edwardfoofoo14/ALICE-keyboard-/PCB/3d/keycap/DSA_2u.step

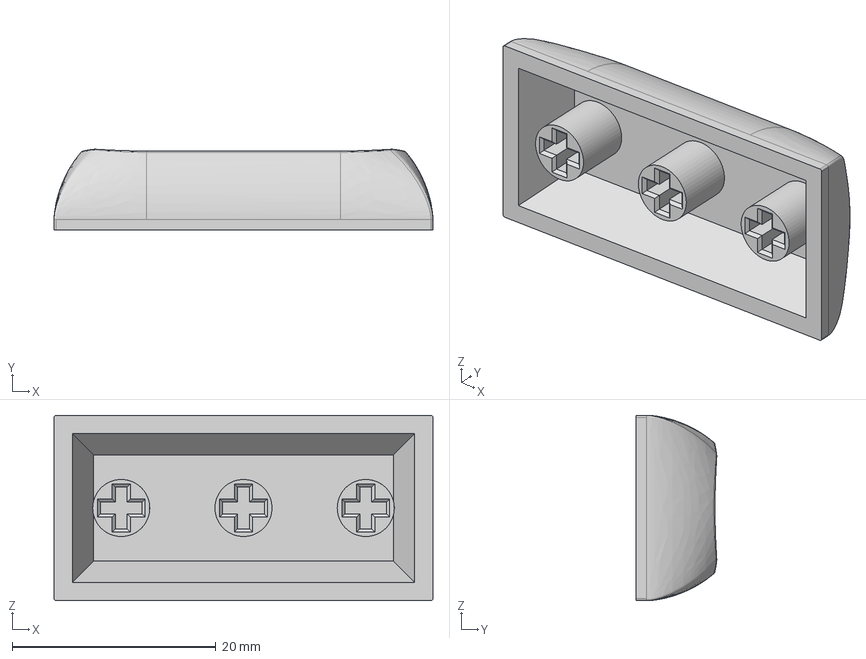
[picture p20: CAD file, 2026-01-05]
PCB/3d/keycap/DSA_2u.step
37.2 x 7.91 x 18.2 mm
