edwardfoofoo14/ALICE-keyboard-/PCB/3d/switch.step

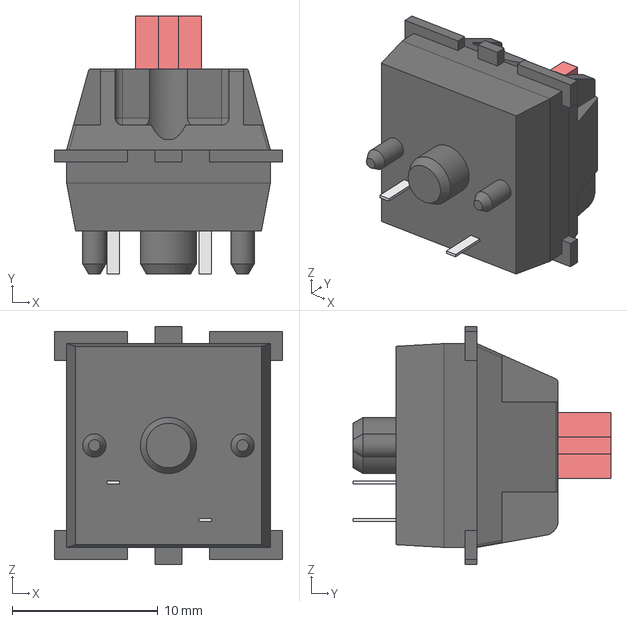
[picture p21: CAD file, 2026-01-05]
PCB/3d/switch.step
15.6 x 17.7 x 16.3 mm
