edwardfoofoo14/ALICE-keyboard-/production/LaserCut/plate 8.dxf

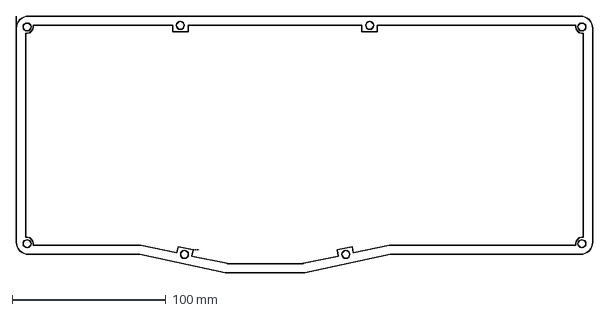
[picture p22: CAD file, 2025-12-23]
production/LaserCut/plate 8.dxf
375.0 x 167.0 mm
