edwardfoofoo14/ALICE-keyboard-/PCB/3d/keycap/DSA_2.75u.step

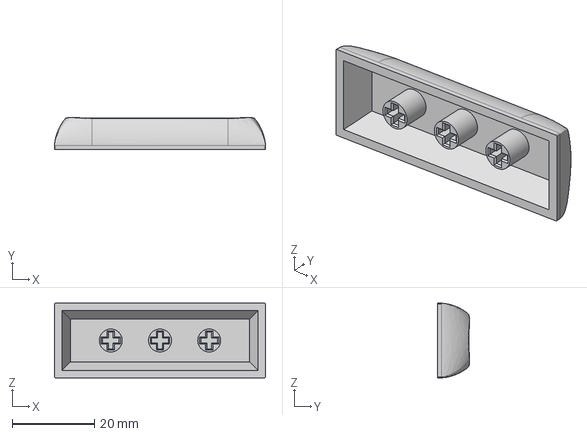
[picture p23: CAD file, 2026-01-05]
PCB/3d/keycap/DSA_2.75u.step
51.5 x 7.91 x 18.2 mm
