edwardfoofoo14/ALICE-keyboard-/PCB/3d/TS-1187A-B-A-B.step

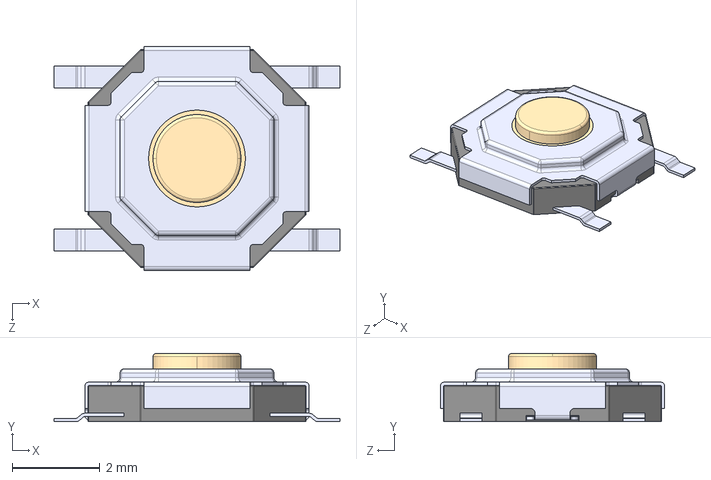
[picture p24: CAD file, 2026-01-05]
PCB/3d/TS-1187A-B-A-B.step
6.50 x 1.55 x 5.10 mm
