edwardfoofoo14/ALICE-keyboard-/PCB/3d/keycap/DSA_1.25u.step

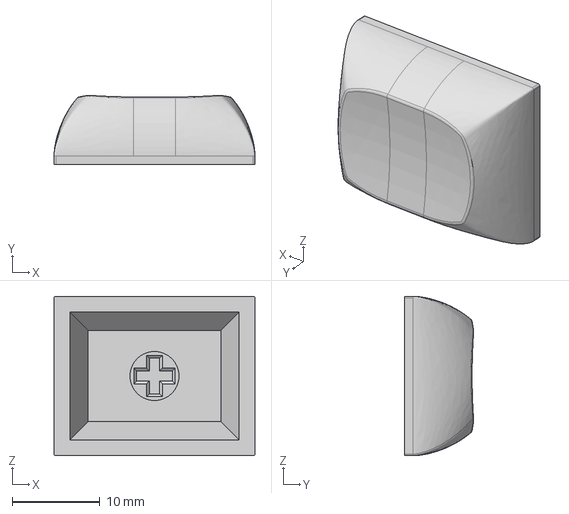
[picture p25: CAD file, 2026-01-05]
PCB/3d/keycap/DSA_1.25u.step
22.9 x 7.91 x 18.2 mm
