edwardfoofoo14/ALICE-keyboard-/PCB/3d/stabilizer.STEP

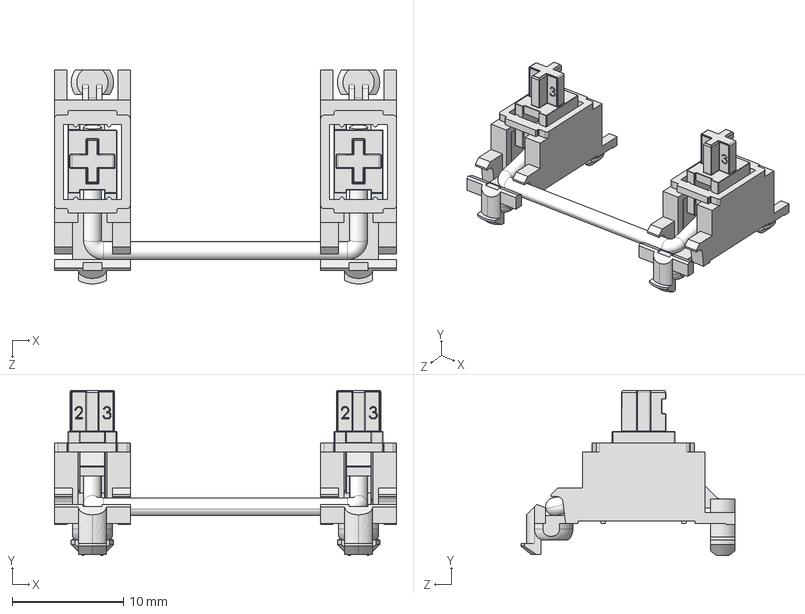
[picture p26: CAD file, 2026-01-05]
PCB/3d/stabilizer.STEP
30.7 x 14.9 x 19.2 mm
mx Stabilizer base 16828 x 2
mx Stabilizer key 16828 x 2
metal stick 16828
