edwardfoofoo14/ALICE-keyboard-/production/LaserCut/plate 10.dxf

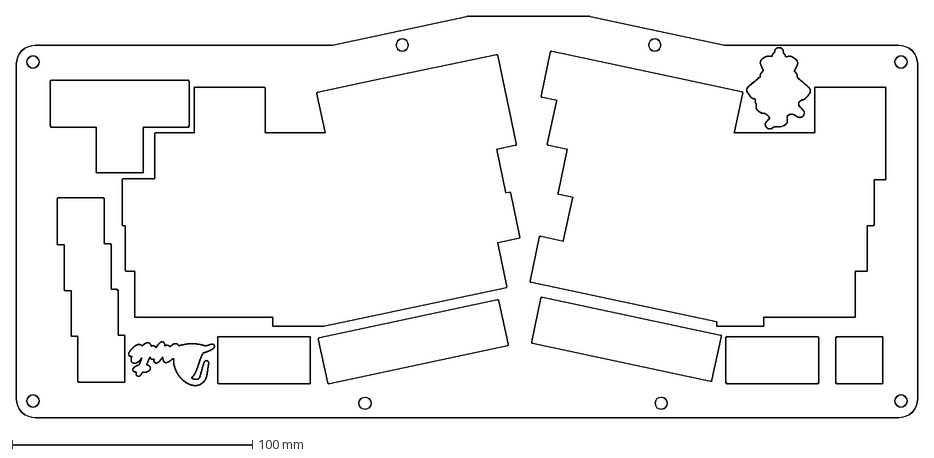
[picture p28: CAD file, 2025-12-23]
production/LaserCut/plate 10.dxf
375.0 x 167.0 mm
