edwardfoofoo14/ALICE-keyboard-/PCB/thisoneinitiald.kicad_sch

## KiCad design PCB/thisoneinitiald.kicad_sch (2026-01-20)

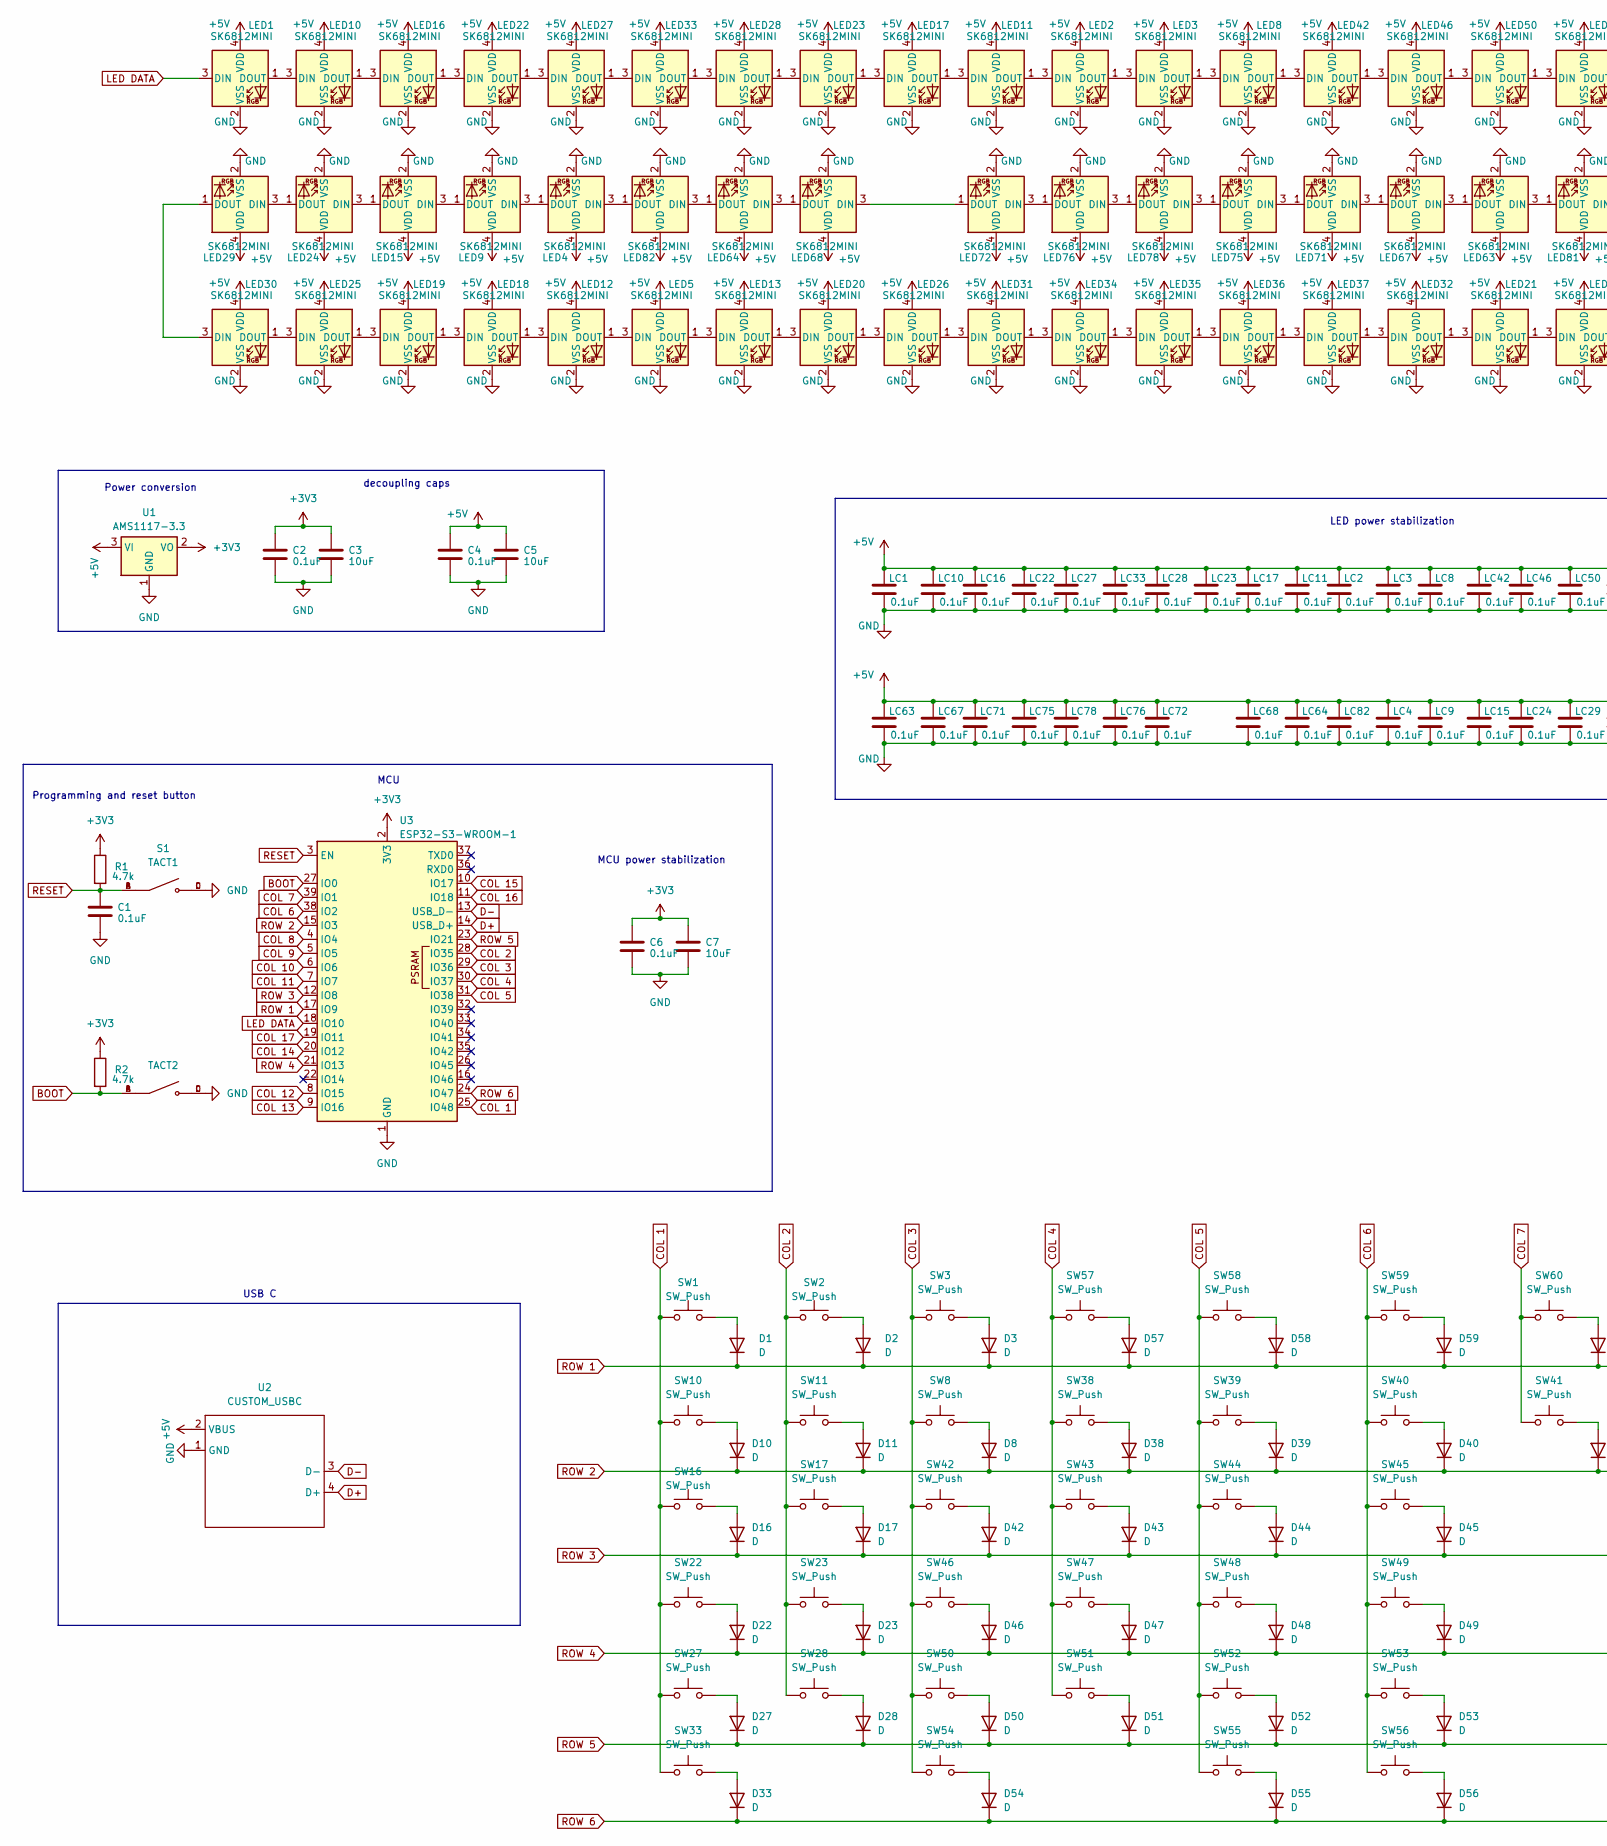
[picture p30: schematic thisoneinitiald.kicad_sch, part in row 1, column 1]

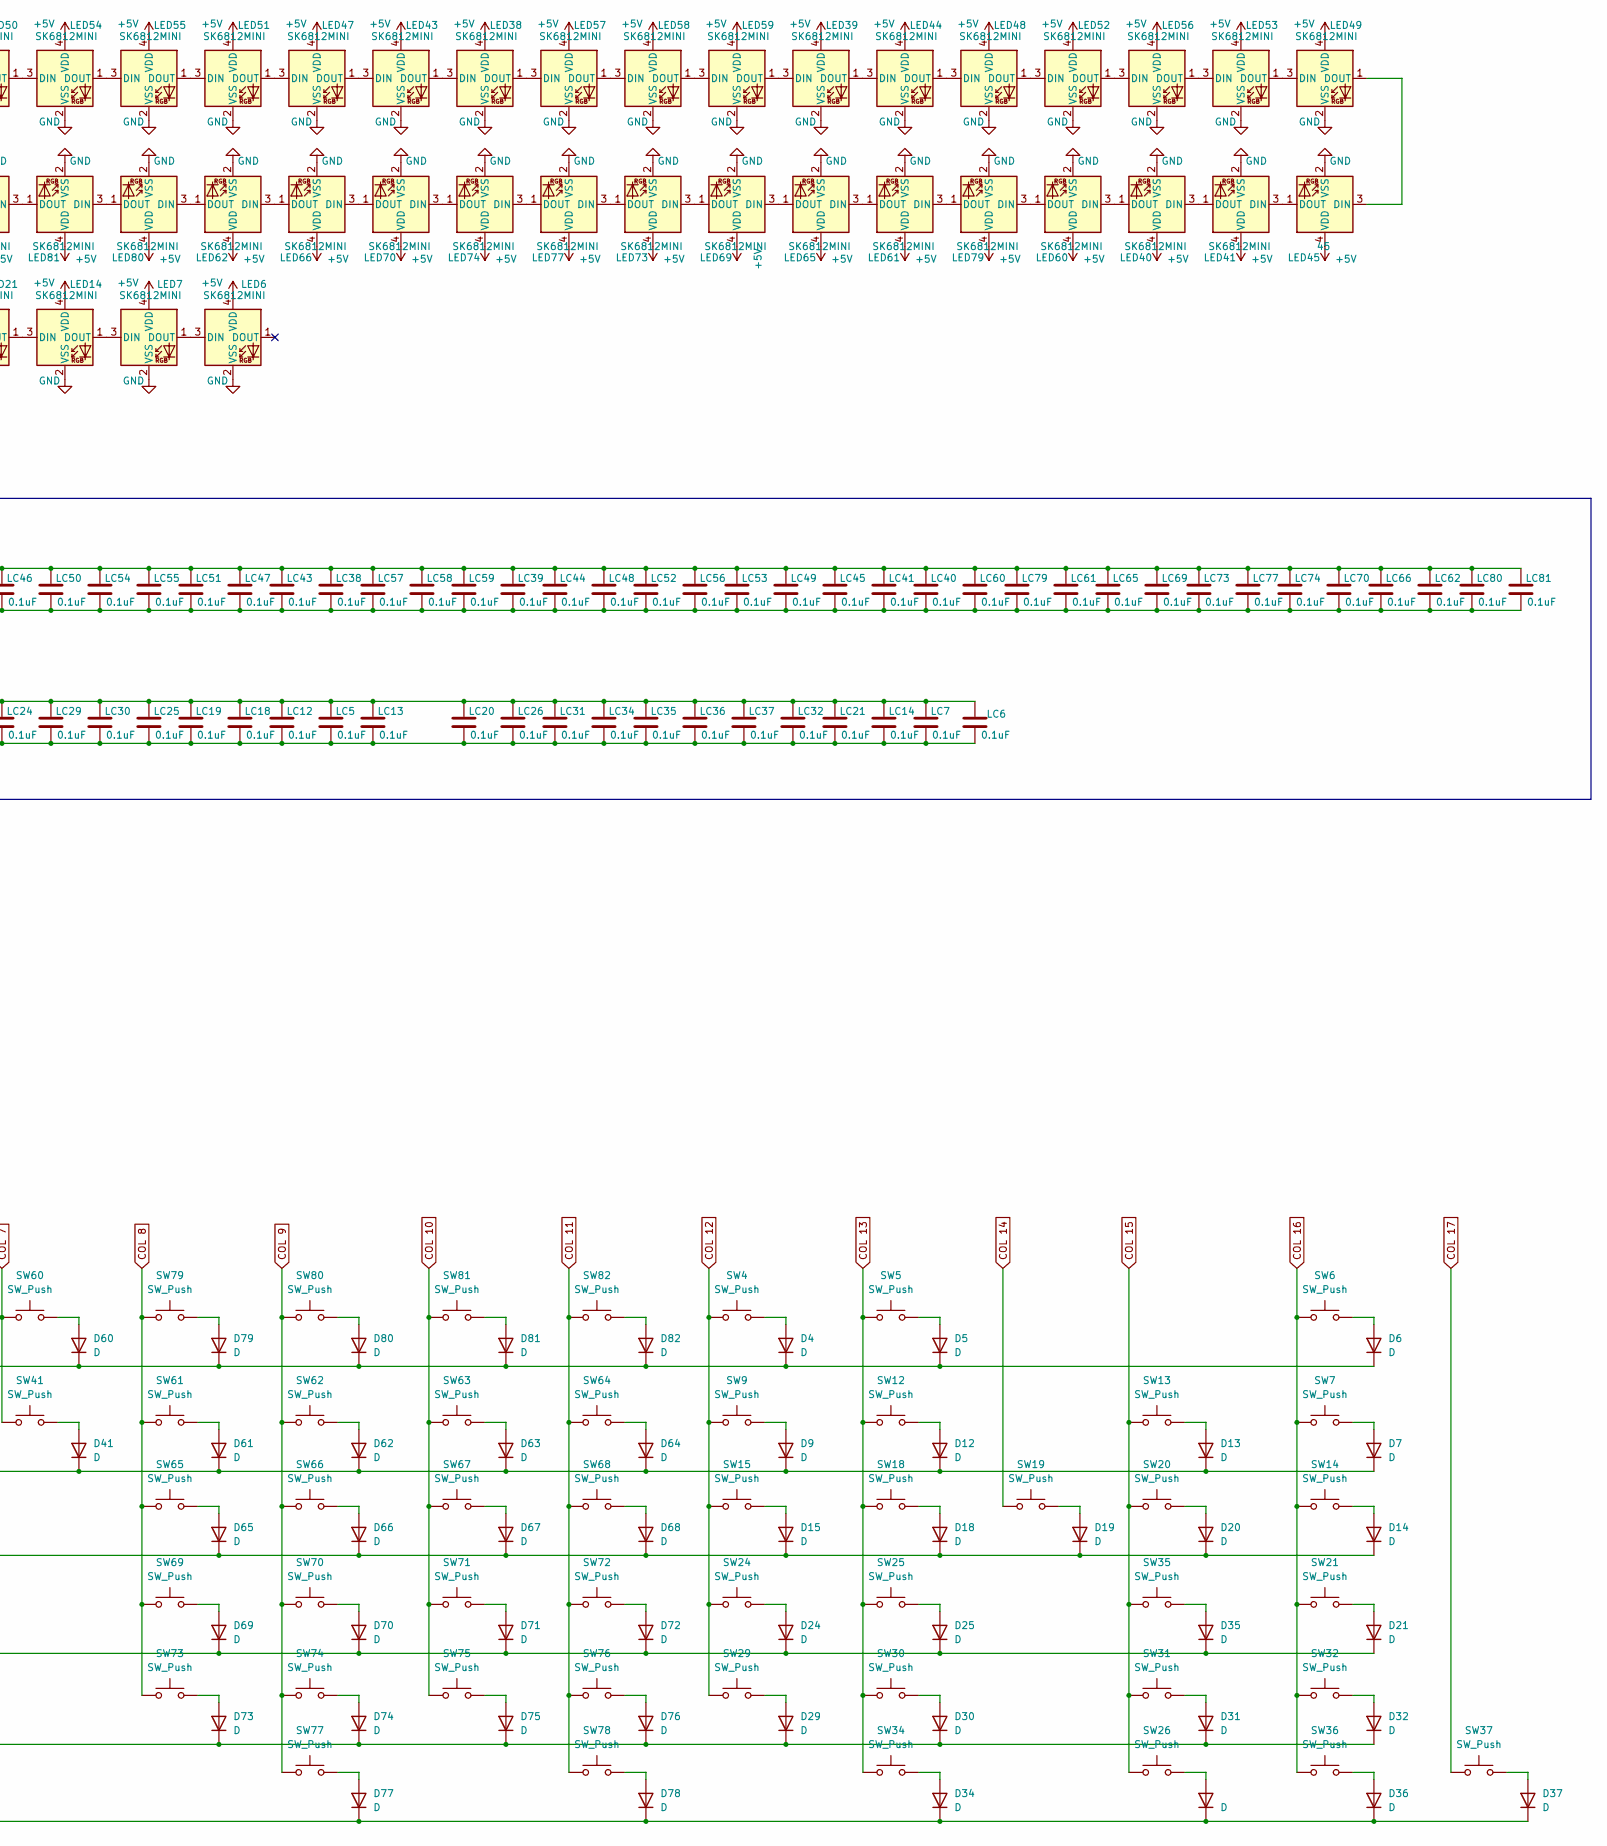
[picture p31: schematic thisoneinitiald.kicad_sch, part in row 1, column 2]

Parts:
C1, C2, C4, C6: 0.1uF; C_1206_3216Metric_Pad1.33x1.80mm_HandSolder
C3, C5, C7: 10uF; C_1206_3216Metric_Pad1.33x1.80mm_HandSolder
D1, D2, D3, D4, D5, D6, D7, D8, D9, D10, D11, D12, D13, D14, D15, D16, D17, D18, D19, D20, D21, D22, D23, D24, D25, D26, D27, D28, D29, D30, D31, D32, D33, D34, D35, D36, D37, D38, D39, D40, D41, D42, D43, D44, D45, D46, D47, D48, D49, D50, D51, D52, D53, D54, D55, D56, D57, D58, D59, D60, D61, D62, D63, D64, D65, D66, D67, D68, D69, D70, D71, D72, D73, D74, D75, D76, D77, D78, D79, D80, D81, D82: D; D_SOD-123F
LC1, LC2, LC3, LC4, LC5, LC6, LC7, LC8, LC9, LC10, LC11, LC12, LC13, LC14, LC15, LC16, LC17, LC18, LC19, LC20, LC21, LC22, LC23, LC24, LC25, LC26, LC27, LC28, LC29, LC30, LC31, LC32, LC33, LC34, LC35, LC36, LC37, LC38, LC39, LC40, LC41, LC42, LC43, LC44, LC45, LC46, LC47, LC48, LC49, LC50, LC51, LC52, LC53, LC54, LC55, LC56, LC57, LC58, LC59, LC60, LC61, LC62, LC63, LC64, LC65, LC66, LC67, LC68, LC69, LC70, LC71, LC72, LC73, LC74, LC75, LC76, LC77, LC78, LC79, LC80, LC81, LC82: 0.1uF; C_1206_3216Metric_Pad1.33x1.80mm_HandSolder
LED1, LED2, LED3, LED4, LED5, LED6, LED7, LED8, LED9, LED10, LED11, LED12, LED13, LED14, LED15, LED16, LED17, LED18, LED19, LED20, LED21, LED22, LED23, LED24, LED25, LED26, LED27, LED28, LED29, LED30, LED31, LED32, LED33, LED34, LED35, LED36, LED37, LED38, LED39, LED40, LED41, LED42, LED43, LED44, LED46, LED47, LED48, LED49, LED50, LED51, LED52, LED53, LED54, LED55, LED56, LED57, LED58, LED59, LED60, LED61, LED62, LED63, LED64, LED65, LED66, LED67, LED68, LED69, LED70, LED71, LED72, LED73, LED74, LED75, LED76, LED77, LED78, LED79, LED80, LED81, LED82: SK6812MINI; SK6812MINI-E
LED45: 45; SK6812MINI-E
R1, R2: 4.7k; C_1206_3216Metric_Pad1.33x1.80mm_HandSolder
S1: TACT1; SW_TS-1187A-B-A-B; PARTREV A0
S2: TACT2; SW_TS-1187A-B-A-B; PARTREV A0
SW1, SW2, SW3, SW4, SW5, SW6, SW7, SW8, SW9, SW10, SW11, SW12, SW14, SW15, SW17, SW18, SW19, SW21, SW23, SW24, SW25, SW26, SW28, SW29, SW30, SW32, SW36, SW37, SW38, SW39, SW40, SW41, SW42, SW43, SW44, SW45, SW46, SW47, SW48, SW49, SW50, SW51, SW52, SW53, SW56, SW57, SW58, SW59, SW60, SW61, SW62, SW63, SW64, SW65, SW66, SW67, SW68, SW69, SW70, SW71, SW72, SW73, SW74, SW75, SW76, SW79, SW80, SW81, SW82: SW_Push; SW_Hotswap_Kailh_MX_Plated_1.00u
SW13, SW55: SW_Push; SW_Hotswap_Kailh_MX_Plated_2.00u
SW16, SW20, SW33, SW34: SW_Push; SW_Hotswap_Kailh_MX_Plated_1.50u
SW22, SW31: SW_Push; SW_Hotswap_Kailh_MX_Plated_1.75u
SW27, SW35: SW_Push; SW_Hotswap_Kailh_MX_Plated_2.25u
SW54, SW78: SW_Push; SW_Hotswap_Kailh_MX_Plated_1.25u
SW77: SW_Push; SW_Hotswap_Kailh_MX_Plated_2.75u
U1: AMS1117-3.3; SOT-223-3_TabPin2
U2: CUSTOM_USBC
U3: ESP32-S3-WROOM-1

Connections:
+3V3: C2.1, C3.1, C6.1, C7.1, R1.1, R2.1, U1.2 (VO), U3.2 (3V3)
+5V: C4.1, C5.1, LC1.1, LC2.1, LC3.1, LC4.1, LC5.1, LC6.1, LC7.1, LC8.1, LC9.1, LC10.1, LC11.1, LC12.1, LC13.1, LC14.1, LC15.1, LC16.1, LC17.1, LC18.1, LC19.1, LC20.1, LC21.1, LC22.1, LC23.1, LC24.1, LC25.1, LC26.1, LC27.1, LC28.1, LC29.1, LC30.1, LC31.1, LC32.1, LC33.1, LC34.1, LC35.1, LC36.1, LC37.1, LC38.1, LC39.1, LC40.1, LC41.1, LC42.1, LC43.1, LC44.1, LC45.1, LC46.1, LC47.1, LC48.1, LC49.1, LC50.1, LC51.1, LC52.1, LC53.1, LC54.1, LC55.1, LC56.1, LC57.1, LC58.1, LC59.1, LC60.1, LC61.1, LC62.1, LC63.1, LC64.1, LC65.1, LC66.1, LC67.1, LC68.1, LC69.1, LC70.1, LC71.1, LC72.1, LC73.1, LC74.1, LC75.1, LC76.1, LC77.1, LC78.1, LC79.1, LC80.1, LC81.1, LC82.1, LED1.4 (VDD), LED2.4 (VDD), LED3.4 (VDD), LED4.4 (VDD), LED5.4 (VDD), LED6.4 (VDD), LED7.4 (VDD), LED8.4 (VDD), LED9.4 (VDD), LED10.4 (VDD), LED11.4 (VDD), LED12.4 (VDD), LED13.4 (VDD), LED14.4 (VDD), LED15.4 (VDD), LED16.4 (VDD), LED17.4 (VDD), LED18.4 (VDD), LED19.4 (VDD), LED20.4 (VDD), LED21.4 (VDD), LED22.4 (VDD), LED23.4 (VDD), LED24.4 (VDD), LED25.4 (VDD), LED26.4 (VDD), LED27.4 (VDD), LED28.4 (VDD), LED29.4 (VDD), LED30.4 (VDD), LED31.4 (VDD), LED32.4 (VDD), LED33.4 (VDD), LED34.4 (VDD), LED35.4 (VDD), LED36.4 (VDD), LED37.4 (VDD), LED38.4 (VDD), LED39.4 (VDD), LED40.4 (VDD), LED41.4 (VDD), LED42.4 (VDD), LED43.4 (VDD), LED44.4 (VDD), LED45.4 (VDD), LED46.4 (VDD), LED47.4 (VDD), LED48.4 (VDD), LED49.4 (VDD), LED50.4 (VDD), LED51.4 (VDD), LED52.4 (VDD), LED53.4 (VDD), LED54.4 (VDD), LED55.4 (VDD), LED56.4 (VDD), LED57.4 (VDD), LED58.4 (VDD), LED59.4 (VDD), LED60.4 (VDD), LED61.4 (VDD), LED62.4 (VDD), LED63.4 (VDD), LED64.4 (VDD), LED65.4 (VDD), LED66.4 (VDD), LED67.4 (VDD), LED68.4 (VDD), LED69.4 (VDD), LED70.4 (VDD), LED71.4 (VDD), LED72.4 (VDD), LED73.4 (VDD), LED74.4 (VDD), LED75.4 (VDD), LED76.4 (VDD), LED77.4 (VDD), LED78.4 (VDD), LED79.4 (VDD), LED80.4 (VDD), LED81.4 (VDD), LED82.4 (VDD), U1.3 (VI), U2.2 (VBUS)
BOOT: R2.2, S2.A, S2.B, U3.27 (IO0)
COL 1: SW1.1, SW10.1, SW16.1, SW22.1, SW27.1, SW33.1, U3.25 (IO48)
COL 2: SW2.1, SW11.1, SW17.1, SW23.1, SW28.1, U3.28 (IO35)
COL 3: SW3.1, SW8.1, SW42.1, SW46.1, SW50.1, SW54.1, U3.29 (IO36)
COL 4: SW38.1, SW43.1, SW47.1, SW51.1, SW57.1, U3.30 (IO37)
COL 5: SW39.1, SW44.1, SW48.1, SW52.1, SW55.1, SW58.1, U3.31 (IO38)
COL 6: SW40.1, SW45.1, SW49.1, SW53.1, SW56.1, SW59.1, U3.38 (IO2)
COL 7: SW41.1, SW60.1, U3.39 (IO1)
COL 8: SW61.1, SW65.1, SW69.1, SW73.1, SW79.1, U3.4 (IO4)
COL 9: SW62.1, SW66.1, SW70.1, SW74.1, SW77.1, SW80.1, U3.5 (IO5)
COL 10: SW63.1, SW67.1, SW71.1, SW75.1, SW81.1, U3.6 (IO6)
COL 11: SW64.1, SW68.1, SW72.1, SW76.1, SW78.1, SW82.1, U3.7 (IO7)
COL 12: SW4.1, SW9.1, SW15.1, SW24.1, SW29.1, U3.8 (IO15)
COL 13: SW5.1, SW12.1, SW18.1, SW25.1, SW30.1, SW34.1, U3.9 (IO16)
COL 14: SW19.1, U3.20 (IO12)
COL 15: SW13.1, SW20.1, SW26.1, SW31.1, SW35.1, U3.10 (IO17)
COL 16: SW6.1, SW7.1, SW14.1, SW21.1, SW32.1, SW36.1, U3.11 (IO18)
COL 17: SW37.1, U3.19 (IO11)
D+: U2.4 (D+), U3.14 (USB_D+)
D-: U2.3 (D-), U3.13 (USB_D-)
GND: C1.2, C2.2, C3.2, C4.2, C5.2, C6.2, C7.2, LC1.2, LC2.2, LC3.2, LC4.2, LC5.2, LC6.2, LC7.2, LC8.2, LC9.2, LC10.2, LC11.2, LC12.2, LC13.2, LC14.2, LC15.2, LC16.2, LC17.2, LC18.2, LC19.2, LC20.2, LC21.2, LC22.2, LC23.2, LC24.2, LC25.2, LC26.2, LC27.2, LC28.2, LC29.2, LC30.2, LC31.2, LC32.2, LC33.2, LC34.2, LC35.2, LC36.2, LC37.2, LC38.2, LC39.2, LC40.2, LC41.2, LC42.2, LC43.2, LC44.2, LC45.2, LC46.2, LC47.2, LC48.2, LC49.2, LC50.2, LC51.2, LC52.2, LC53.2, LC54.2, LC55.2, LC56.2, LC57.2, LC58.2, LC59.2, LC60.2, LC61.2, LC62.2, LC63.2, LC64.2, LC65.2, LC66.2, LC67.2, LC68.2, LC69.2, LC70.2, LC71.2, LC72.2, LC73.2, LC74.2, LC75.2, LC76.2, LC77.2, LC78.2, LC79.2, LC80.2, LC81.2, LC82.2, LED1.2 (VSS), LED2.2 (VSS), LED3.2 (VSS), LED4.2 (VSS), LED5.2 (VSS), LED6.2 (VSS), LED7.2 (VSS), LED8.2 (VSS), LED9.2 (VSS), LED10.2 (VSS), LED11.2 (VSS), LED12.2 (VSS), LED13.2 (VSS), LED14.2 (VSS), LED15.2 (VSS), LED16.2 (VSS), LED17.2 (VSS), LED18.2 (VSS), LED19.2 (VSS), LED20.2 (VSS), LED21.2 (VSS), LED22.2 (VSS), LED23.2 (VSS), LED24.2 (VSS), LED25.2 (VSS), LED26.2 (VSS), LED27.2 (VSS), LED28.2 (VSS), LED29.2 (VSS), LED30.2 (VSS), LED31.2 (VSS), LED32.2 (VSS), LED33.2 (VSS), LED34.2 (VSS), LED35.2 (VSS), LED36.2 (VSS), LED37.2 (VSS), LED38.2 (VSS), LED39.2 (VSS), LED40.2 (VSS), LED41.2 (VSS), LED42.2 (VSS), LED43.2 (VSS), LED44.2 (VSS), LED45.2 (VSS), LED46.2 (VSS), LED47.2 (VSS), LED48.2 (VSS), LED49.2 (VSS), LED50.2 (VSS), LED51.2 (VSS), LED52.2 (VSS), LED53.2 (VSS), LED54.2 (VSS), LED55.2 (VSS), LED56.2 (VSS), LED57.2 (VSS), LED58.2 (VSS), LED59.2 (VSS), LED60.2 (VSS), LED61.2 (VSS), LED62.2 (VSS), LED63.2 (VSS), LED64.2 (VSS), LED65.2 (VSS), LED66.2 (VSS), LED67.2 (VSS), LED68.2 (VSS), LED69.2 (VSS), LED70.2 (VSS), LED71.2 (VSS), LED72.2 (VSS), LED73.2 (VSS), LED74.2 (VSS), LED75.2 (VSS), LED76.2 (VSS), LED77.2 (VSS), LED78.2 (VSS), LED79.2 (VSS), LED80.2 (VSS), LED81.2 (VSS), LED82.2 (VSS), S1.C, S1.D, S2.C, S2.D, U1.1 (GND), U2.1 (GND), U3.1 (GND), U3.40 (GND), U3.41 (GND)
LED DATA: LED1.3 (DIN), U3.18 (IO10)
unnamed: D1.2 (A), SW1.2
unnamed: D2.2 (A), SW2.2
unnamed: D3.2 (A), SW3.2
unnamed: D4.2 (A), SW4.2
unnamed: D5.2 (A), SW5.2
unnamed: D6.2 (A), SW6.2
unnamed: D7.2 (A), SW7.2
unnamed: D8.2 (A), SW8.2
unnamed: D9.2 (A), SW9.2
unnamed: D10.2 (A), SW10.2
unnamed: D11.2 (A), SW11.2
unnamed: D12.2 (A), SW12.2
unnamed: D13.2 (A), SW13.2
unnamed: D14.2 (A), SW14.2
unnamed: D15.2 (A), SW15.2
unnamed: D16.2 (A), SW16.2
unnamed: D17.2 (A), SW17.2
unnamed: D18.2 (A), SW18.2
unnamed: D19.2 (A), SW19.2
unnamed: D20.2 (A), SW20.2
unnamed: D21.2 (A), SW21.2
unnamed: D22.2 (A), SW22.2
unnamed: D23.2 (A), SW23.2
unnamed: D24.2 (A), SW24.2
unnamed: D25.2 (A), SW25.2
unnamed: D26.2 (A), SW26.2
unnamed: D27.2 (A), SW27.2
unnamed: D28.2 (A), SW28.2
unnamed: D29.2 (A), SW29.2
unnamed: D30.2 (A), SW30.2
unnamed: D31.2 (A), SW31.2
unnamed: D32.2 (A), SW32.2
unnamed: D33.2 (A), SW33.2
unnamed: D34.2 (A), SW34.2
unnamed: D35.2 (A), SW35.2
unnamed: D36.2 (A), SW36.2
unnamed: D37.2 (A), SW37.2
unnamed: D38.2 (A), SW38.2
unnamed: D39.2 (A), SW39.2
unnamed: D40.2 (A), SW40.2
unnamed: D41.2 (A), SW41.2
unnamed: D42.2 (A), SW42.2
unnamed: D43.2 (A), SW43.2
unnamed: D44.2 (A), SW44.2
unnamed: D45.2 (A), SW45.2
unnamed: D46.2 (A), SW46.2
unnamed: D47.2 (A), SW47.2
unnamed: D48.2 (A), SW48.2
unnamed: D49.2 (A), SW49.2
unnamed: D50.2 (A), SW50.2
unnamed: D51.2 (A), SW51.2
unnamed: D52.2 (A), SW52.2
unnamed: D53.2 (A), SW53.2
unnamed: D54.2 (A), SW54.2
unnamed: D55.2 (A), SW55.2
unnamed: D56.2 (A), SW56.2
unnamed: D57.2 (A), SW57.2
unnamed: D58.2 (A), SW58.2
unnamed: D59.2 (A), SW59.2
unnamed: D60.2 (A), SW60.2
unnamed: D61.2 (A), SW61.2
unnamed: D62.2 (A), SW62.2
unnamed: D63.2 (A), SW63.2
unnamed: D64.2 (A), SW64.2
unnamed: D65.2 (A), SW65.2
unnamed: D66.2 (A), SW66.2
unnamed: D67.2 (A), SW67.2
unnamed: D68.2 (A), SW68.2
unnamed: D69.2 (A), SW69.2
unnamed: D70.2 (A), SW70.2
unnamed: D71.2 (A), SW71.2
unnamed: D72.2 (A), SW72.2
unnamed: D73.2 (A), SW73.2
unnamed: D74.2 (A), SW74.2
unnamed: D75.2 (A), SW75.2
unnamed: D76.2 (A), SW76.2
unnamed: D77.2 (A), SW77.2
unnamed: D78.2 (A), SW78.2
unnamed: D79.2 (A), SW79.2
unnamed: D80.2 (A), SW80.2
unnamed: D81.2 (A), SW81.2
unnamed: D82.2 (A), SW82.2
unnamed: LED1.1 (DOUT), LED10.3 (DIN)
unnamed: LED2.1 (DOUT), LED3.3 (DIN)
unnamed: LED3.1 (DOUT), LED8.3 (DIN)
unnamed: LED4.1 (DOUT), LED9.3 (DIN)
unnamed: LED4.3 (DIN), LED82.1 (DOUT)
unnamed: LED6.3 (DIN), LED7.1 (DOUT)
unnamed: LED10.1 (DOUT), LED16.3 (DIN)
unnamed: LED2.3 (DIN), LED11.1 (DOUT)
unnamed: LED11.3 (DIN), LED17.1 (DOUT)
unnamed: LED5.3 (DIN), LED12.1 (DOUT)
unnamed: LED12.3 (DIN), LED18.1 (DOUT)
unnamed: LED13.1 (DOUT), LED20.3 (DIN)
unnamed: LED5.1 (DOUT), LED13.3 (DIN)
unnamed: LED7.3 (DIN), LED14.1 (DOUT)
unnamed: LED14.3 (DIN), LED21.1 (DOUT)
unnamed: LED15.1 (DOUT), LED24.3 (DIN)
unnamed: LED9.1 (DOUT), LED15.3 (DIN)
unnamed: LED16.1 (DOUT), LED22.3 (DIN)
unnamed: LED17.3 (DIN), LED23.1 (DOUT)
unnamed: LED18.3 (DIN), LED19.1 (DOUT)
unnamed: LED19.3 (DIN), LED25.1 (DOUT)
unnamed: LED20.1 (DOUT), LED26.3 (DIN)
unnamed: LED21.3 (DIN), LED32.1 (DOUT)
unnamed: LED22.1 (DOUT), LED27.3 (DIN)
unnamed: LED23.3 (DIN), LED28.1 (DOUT)
unnamed: LED24.1 (DOUT), LED29.3 (DIN)
unnamed: LED25.3 (DIN), LED30.1 (DOUT)
unnamed: LED26.1 (DOUT), LED31.3 (DIN)
unnamed: LED27.1 (DOUT), LED33.3 (DIN)
unnamed: LED28.3 (DIN), LED33.1 (DOUT)
unnamed: LED29.1 (DOUT), LED30.3 (DIN)
unnamed: LED31.1 (DOUT), LED34.3 (DIN)
unnamed: LED32.3 (DIN), LED37.1 (DOUT)
unnamed: LED34.1 (DOUT), LED35.3 (DIN)
unnamed: LED35.1 (DOUT), LED36.3 (DIN)
unnamed: LED36.1 (DOUT), LED37.3 (DIN)
unnamed: LED38.1 (DOUT), LED57.3 (DIN)
unnamed: LED38.3 (DIN), LED43.1 (DOUT)
unnamed: LED39.1 (DOUT), LED44.3 (DIN)
unnamed: LED39.3 (DIN), LED59.1 (DOUT)
unnamed: LED40.1 (DOUT), LED60.3 (DIN)
unnamed: LED40.3 (DIN), LED41.1 (DOUT)
unnamed: LED41.3 (DIN), LED45.1 (DOUT)
unnamed: LED42.1 (DOUT), LED46.3 (DIN)
unnamed: LED8.1 (DOUT), LED42.3 (DIN)
unnamed: LED43.3 (DIN), LED47.1 (DOUT)
unnamed: LED44.1 (DOUT), LED48.3 (DIN)
unnamed: LED45.3 (DIN), LED49.1 (DOUT)
unnamed: LED46.1 (DOUT), LED50.3 (DIN)
unnamed: LED47.3 (DIN), LED51.1 (DOUT)
unnamed: LED48.1 (DOUT), LED52.3 (DIN)
unnamed: LED49.3 (DIN), LED53.1 (DOUT)
unnamed: LED50.1 (DOUT), LED54.3 (DIN)
unnamed: LED51.3 (DIN), LED55.1 (DOUT)
unnamed: LED52.1 (DOUT), LED56.3 (DIN)
unnamed: LED53.3 (DIN), LED56.1 (DOUT)
unnamed: LED54.1 (DOUT), LED55.3 (DIN)
unnamed: LED57.1 (DOUT), LED58.3 (DIN)
unnamed: LED58.1 (DOUT), LED59.3 (DIN)
unnamed: LED60.1 (DOUT), LED79.3 (DIN)
unnamed: LED61.1 (DOUT), LED65.3 (DIN)
unnamed: LED61.3 (DIN), LED79.1 (DOUT)
unnamed: LED62.1 (DOUT), LED80.3 (DIN)
unnamed: LED62.3 (DIN), LED66.1 (DOUT)
unnamed: LED63.1 (DOUT), LED67.3 (DIN)
unnamed: LED63.3 (DIN), LED81.1 (DOUT)
unnamed: LED64.1 (DOUT), LED82.3 (DIN)
unnamed: LED64.3 (DIN), LED68.1 (DOUT)
unnamed: LED65.1 (DOUT), LED69.3 (DIN)
unnamed: LED66.3 (DIN), LED70.1 (DOUT)
unnamed: LED67.1 (DOUT), LED71.3 (DIN)
unnamed: LED68.3 (DIN), LED72.1 (DOUT)
unnamed: LED69.1 (DOUT), LED73.3 (DIN)
unnamed: LED70.3 (DIN), LED74.1 (DOUT)
unnamed: LED71.1 (DOUT), LED75.3 (DIN)
unnamed: LED72.3 (DIN), LED76.1 (DOUT)
unnamed: LED73.1 (DOUT), LED77.3 (DIN)
unnamed: LED74.3 (DIN), LED77.1 (DOUT)
unnamed: LED75.1 (DOUT), LED78.3 (DIN)
unnamed: LED76.3 (DIN), LED78.1 (DOUT)
unnamed: LED80.1 (DOUT), LED81.3 (DIN)
RESET: C1.1, R1.2, S1.A, S1.B, U3.3 (EN)
ROW 1: D1.1 (K), D2.1 (K), D3.1 (K), D4.1 (K), D5.1 (K), D6.1 (K), D57.1 (K), D58.1 (K), D59.1 (K), D60.1 (K), D79.1 (K), D80.1 (K), D81.1 (K), D82.1 (K), U3.17 (IO9)
ROW 2: D7.1 (K), D8.1 (K), D9.1 (K), D10.1 (K), D11.1 (K), D12.1 (K), D13.1 (K), D38.1 (K), D39.1 (K), D40.1 (K), D41.1 (K), D61.1 (K), D62.1 (K), D63.1 (K), D64.1 (K), U3.15 (IO3)
ROW 3: D14.1 (K), D15.1 (K), D16.1 (K), D17.1 (K), D18.1 (K), D19.1 (K), D20.1 (K), D42.1 (K), D43.1 (K), D44.1 (K), D45.1 (K), D65.1 (K), D66.1 (K), D67.1 (K), D68.1 (K), U3.12 (IO8)
ROW 4: D21.1 (K), D22.1 (K), D23.1 (K), D24.1 (K), D25.1 (K), D35.1 (K), D46.1 (K), D47.1 (K), D48.1 (K), D49.1 (K), D69.1 (K), D70.1 (K), D71.1 (K), D72.1 (K), U3.21 (IO13)
ROW 5: D27.1 (K), D28.1 (K), D29.1 (K), D30.1 (K), D31.1 (K), D32.1 (K), D50.1 (K), D51.1 (K), D52.1 (K), D53.1 (K), D73.1 (K), D74.1 (K), D75.1 (K), D76.1 (K), U3.23 (IO21)
ROW 6: D26.1 (K), D33.1 (K), D34.1 (K), D36.1 (K), D37.1 (K), D54.1 (K), D55.1 (K), D56.1 (K), D77.1 (K), D78.1 (K), U3.24 (IO47)

Notes on the sheet:
decoupling caps
MCU power stabilization
LED power stabilization
Programming and reset button
Power conversion
MCU
USB C
